Xenogears/GenericCarController/Case/Case V4.3.png

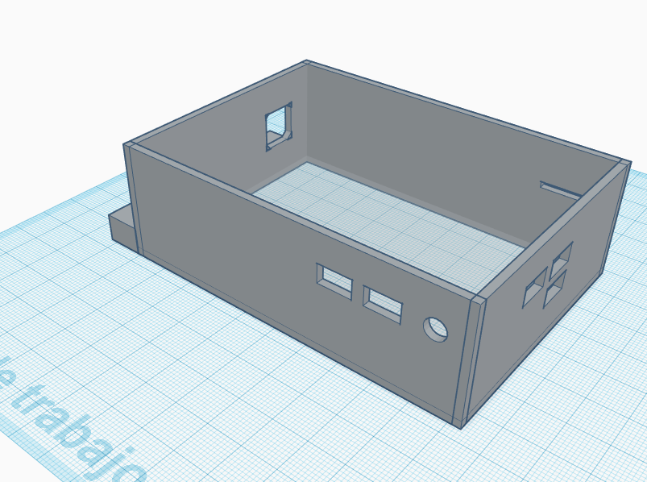
Case/Case V4.3.png
