Xenogears/GenericCarController/Case/Cover V4.3.png

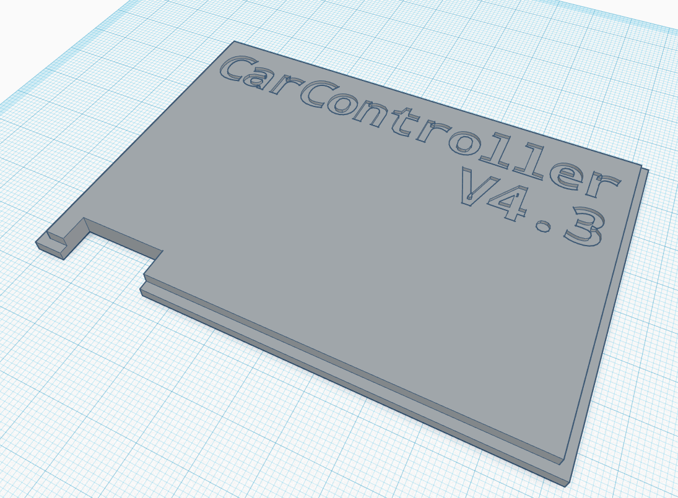
Case/Cover V4.3.png
