Xenogears/GenericCarController/img/v1_back.JPG

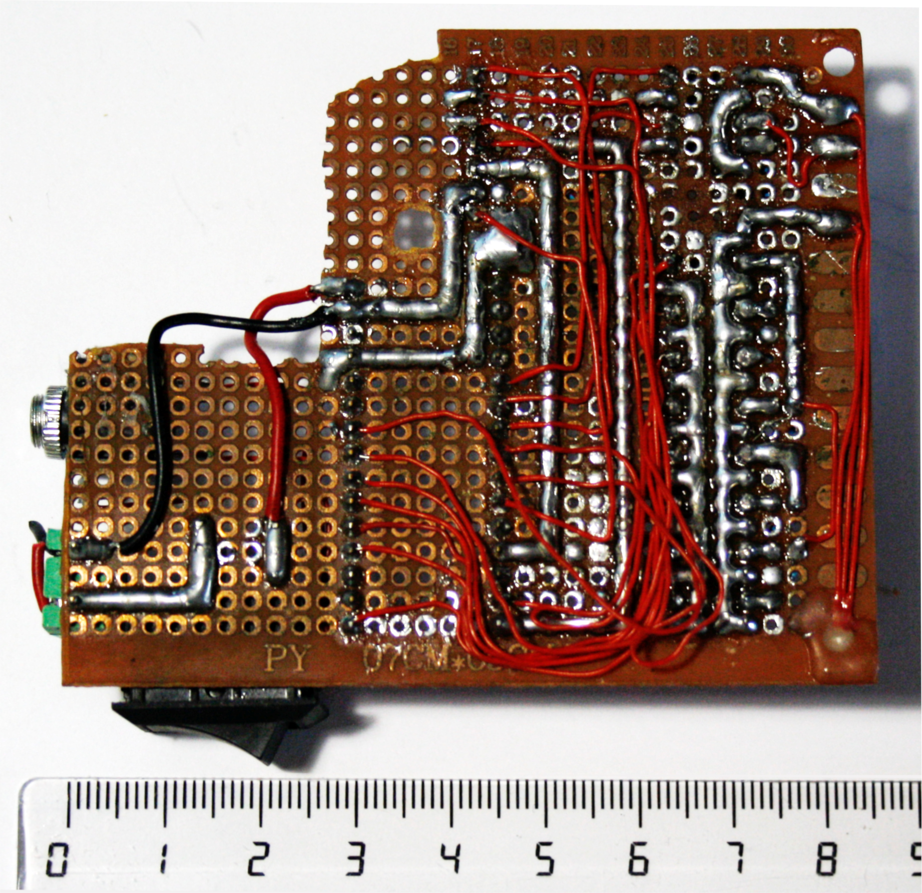
img/v1_back.JPG
