Xenogears/GenericCarController/img/v4_front.JPG

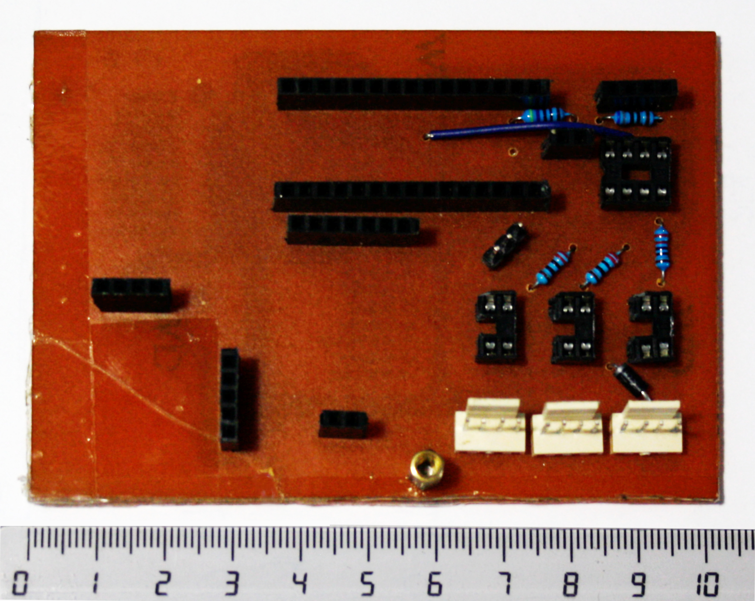
img/v4_front.JPG
