Xenogears/GenericCarController/img/v43_back.JPG

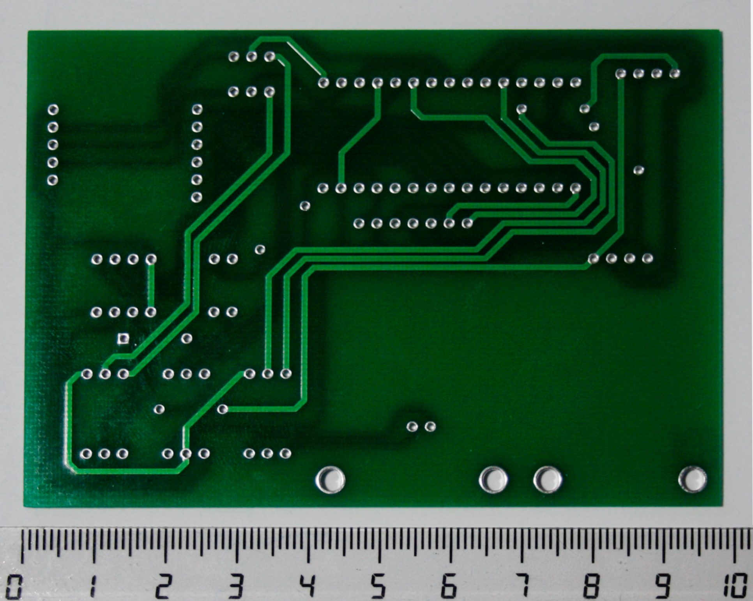
img/v43_back.JPG
