Xenogears/GenericCarController/cars/OpelAstraH2004/astra_h_power.h

//
// Author:	Álvaro Graciá Gil
// License:	This work is licensed under a Creative Commons Attribution-NonCommercial-ShareAlike 4.0 International License 
//	 		(http://creativecommons.org/licenses/by-nc-sa/4.0/) 
//

#ifndef __ASTRA_H_POWER__H__
  #define __ASTRA_H_POWER__H__  
	#include "../../configuration.h"  
	#include "../../power.h"
	#include "../../can_command.h"
	#include "../../radio_command.h"
	#include "../../traccar.h"  
	#include "../../cmd_serial.h"  
	#include "astra_h.h"  
	#include "astra_h_dis.h"   
	#include "astra_h_alarm_led.h"

	#if COMPILE_CAN
		void astraHPowerOnChange(uint8_t previousStatus, uint8_t newStatus);
	#endif
#endif
