Xenogears/GenericCarController/cars/OpelAstraH2004-RPI/constants.cpp

//
// Author:	Álvaro Graciá Gil
// License:	This work is licensed under a Creative Commons Attribution-NonCommercial-ShareAlike 4.0 International License 
//	 		(http://creativecommons.org/licenses/by-nc-sa/4.0/) 
//

#include "constants.h"

#if CAR_MODEL == OPEL_ASTRA_H_2004_MIN_CAR 
	const PROGMEM char sRAD[] = { "RAD" };
	const PROGMEM char sRD[] = { "RD" };
	const PROGMEM char sVolPlus[] = { "vol+" };
	const PROGMEM char sVolMinus[] = { "vol-" };
	const PROGMEM char sNext[] = { "next" };
	const PROGMEM char sPrev[] = { "prev" };
	const PROGMEM char sMute[] = { "mute" };
	const PROGMEM char sDIS_Lower[] = { "dis" };
	const PROGMEM char sSrc[] = { "src" };
	const PROGMEM char sBand[] = { "band" };
	const PROGMEM char sFolderUp[] = { "f_up" };
	const PROGMEM char sFolderDown[] = { "f_down" };
	const PROGMEM char sVoice[] = { "voice" };
	const PROGMEM char sCal[] = { "cal" };
	const PROGMEM char sEcho[] = { "echo" };
#endif
