Xenogears/GenericCarController/constants.cpp

//
// Author:	Álvaro Graciá Gil
// License:	This work is licensed under a Creative Commons Attribution-NonCommercial-ShareAlike 4.0 International License 
//	 		(http://creativecommons.org/licenses/by-nc-sa/4.0/) 
//

#include <avr/pgmspace.h>
#include "constants.h"

const PROGMEM char sRES[] = { "RES" };
const PROGMEM char sENTRY[] = { "ENTRY" };
const PROGMEM char sEquals[] = { "=" };
const PROGMEM char sCAN[] = { "CAN" };
const PROGMEM char sPOT[] = { "POT" };
const PROGMEM char sSTA[] = { "STA" };
const PROGMEM char sTRC[] = { "TRC" };
const PROGMEM char sGSM[] = { "GSM" };
const PROGMEM char sGPS[] = { "GPS" };
const PROGMEM char sALL[] = { "ALL" };
const PROGMEM char sCAR[] = { "CAR" };
const PROGMEM char sDBG[] = { "DBG" };
const PROGMEM char sPOW[] = { "POW" };
const PROGMEM char sOK[] = { "OK" };
const PROGMEM char sERROR[] = { "ERROR" };
const PROGMEM char sZero[] = { "0" };
const PROGMEM char sSpace[] = { " " };
const PROGMEM char sTwoDots[] = { ":" };
const PROGMEM char sComma[] = { "," };
const PROGMEM char sGet[] = { "get" };
const PROGMEM char sSet[] = { "set" };
const PROGMEM char sSave[] = { "save" };
const PROGMEM char sLoad[] = { "load" };
const PROGMEM char sClear[] = { "clear" };
const PROGMEM char sRemove[] = { "remove" };
const PROGMEM char sAdd[] = { "add" };
const PROGMEM char sShow[] = { "show" };
const PROGMEM char sFree[] = { "free" };
const PROGMEM char sReset[] = { "reset" };
const PROGMEM char sWrite[] = { "write" };
const PROGMEM char sLOG[] = { "LOG" };
const PROGMEM char sOPT[] = { "OPT" };
const PROGMEM char sSYS[] = { "SYS" };
const PROGMEM char sROM[] = { "ROM" };
const PROGMEM char sBT[] = { "BT" };
const PROGMEM char sAlarm[] = { "ALARM" };
const PROGMEM char sReceived[] = { "Received" };
const PROGMEM char sSent[] = { "Sent" };
const PROGMEM char sGSMResetSetup[] = { "GSM RST STP" };
const PROGMEM char sGSMGetRetry[] = { "GSM GET RTR" };
const PROGMEM char sGSMRequestMaxErrors[] = { "GSM GET MAX ERR" };
const PROGMEM char sOn[] = { "on" };
const PROGMEM char sOff[] = { "off" };
const PROGMEM char sIn[] = { "in" };
const PROGMEM char sOut[] = { "out" };
const PROGMEM char sWithRing[] = { "Ring" };
const PROGMEM char sSetup[] = { "setup" };
const PROGMEM char sLineFeedLineBreak[] = { "\r\n" };
const PROGMEM char sSpaceCommaSpace[] = { " - " };
const PROGMEM char sSend[] = { "send" };
