Xenogears/GenericCarController/constants.h

//
// Author:	Álvaro Graciá Gil
// License:	This work is licensed under a Creative Commons Attribution-NonCommercial-ShareAlike 4.0 International License 
//	 		(http://creativecommons.org/licenses/by-nc-sa/4.0/) 
//

#include <avr/pgmspace.h>

extern const PROGMEM char sRES[];
extern const PROGMEM char sENTRY[];
extern const PROGMEM char sEquals[];
extern const PROGMEM char sCAN[];
extern const PROGMEM char sPOT[];
extern const PROGMEM char sSTA[];
extern const PROGMEM char sTRC[];
extern const PROGMEM char sGSM[];
extern const PROGMEM char sGPS[];
extern const PROGMEM char sALL[];
extern const PROGMEM char sCAR[];
extern const PROGMEM char sDBG[];
extern const PROGMEM char sPOW[];
extern const PROGMEM char sOK[];
extern const PROGMEM char sERROR[];
extern const PROGMEM char sZero[];
extern const PROGMEM char sSpace[];
extern const PROGMEM char sTwoDots[];
extern const PROGMEM char sComma[];
extern const PROGMEM char sGet[];
extern const PROGMEM char sSet[];
extern const PROGMEM char sSave[];
extern const PROGMEM char sLoad[];
extern const PROGMEM char sClear[];
extern const PROGMEM char sRemove[];
extern const PROGMEM char sAdd[];
extern const PROGMEM char sShow[];
extern const PROGMEM char sFree[];
extern const PROGMEM char sReset[];
extern const PROGMEM char sWrite[];
extern const PROGMEM char sLOG[];
extern const PROGMEM char sOPT[];
extern const PROGMEM char sSYS[];
extern const PROGMEM char sROM[];
extern const PROGMEM char sBT[];
extern const PROGMEM char sAlarm[];
extern const PROGMEM char sReceived[];
extern const PROGMEM char sSent[];
extern const PROGMEM char sGSMResetSetup[];
extern const PROGMEM char sGSMGetRetry[];
extern const PROGMEM char sGSMRequestMaxErrors[];
extern const PROGMEM char sOn[];
extern const PROGMEM char sOff[];
extern const PROGMEM char sIn[];
extern const PROGMEM char sOut[];
extern const PROGMEM char sWithRing[];
extern const PROGMEM char sSetup[];
extern const PROGMEM char sLineFeedLineBreak[];
extern const PROGMEM char sSpaceCommaSpace[];
extern const PROGMEM char sSend[];
